Rexaintreal/HermesHandheld/images/cover.png

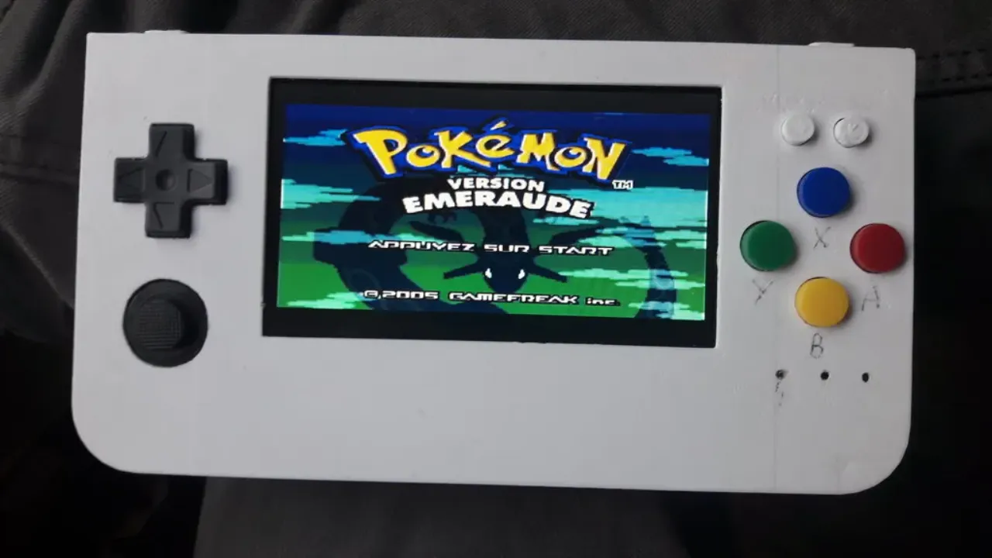
images/cover.png
