Rexaintreal/HermesHandheld/images/inspo.png

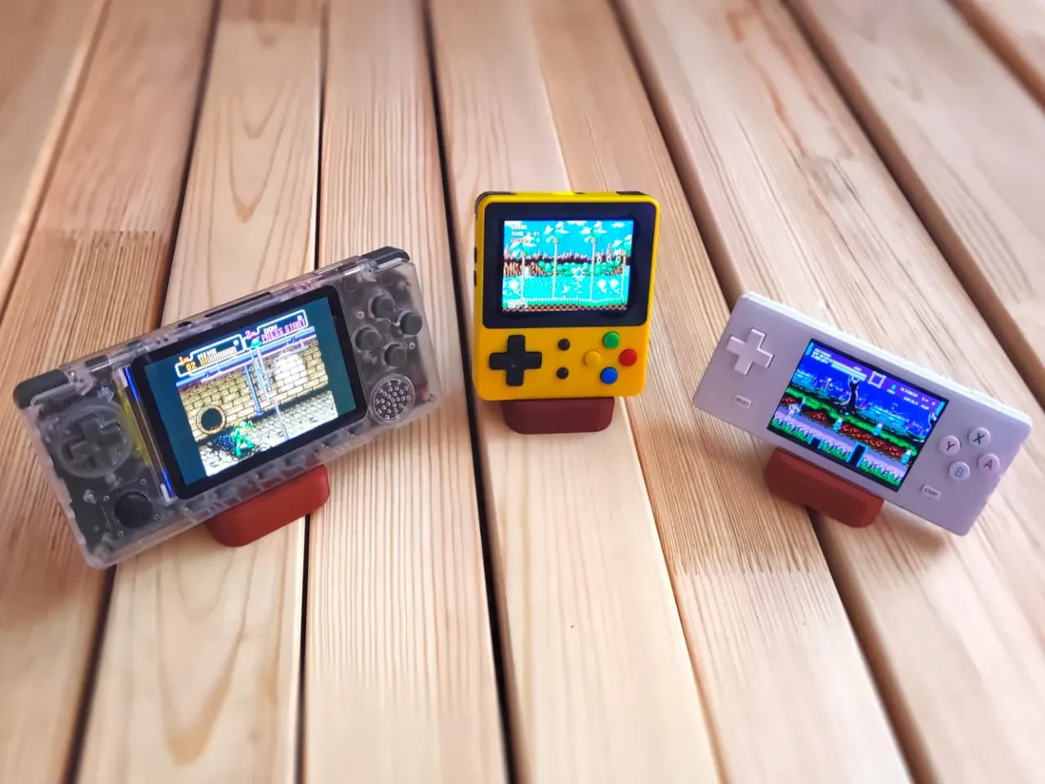
images/inspo.png
