Rexaintreal/HermesHandheld/images/Journal4image3.png

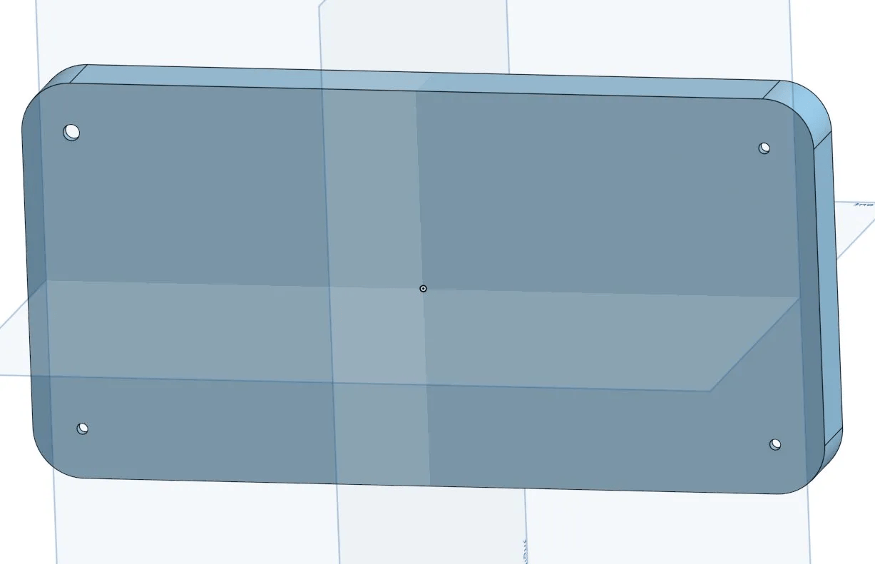
images/Journal4image3.png
