Rexaintreal/HermesHandheld/images/Journal4image4.png

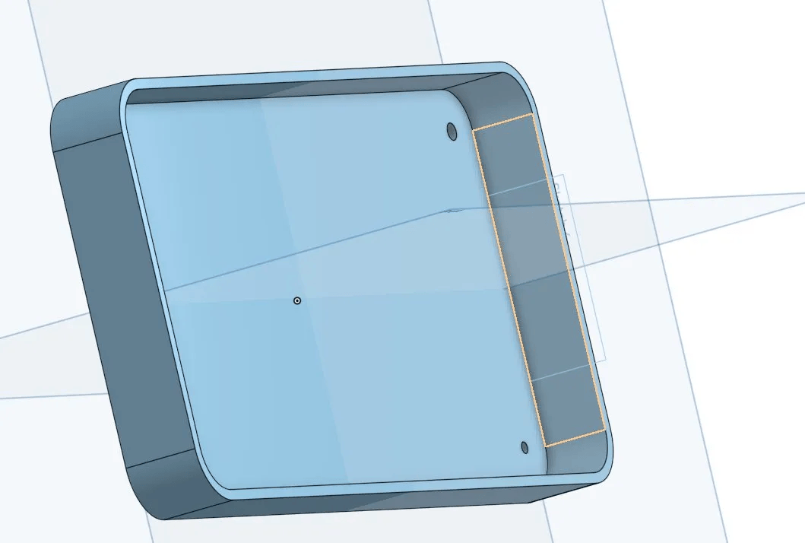
images/Journal4image4.png
