Rexaintreal/HermesHandheld/images/Journal10Image9.png

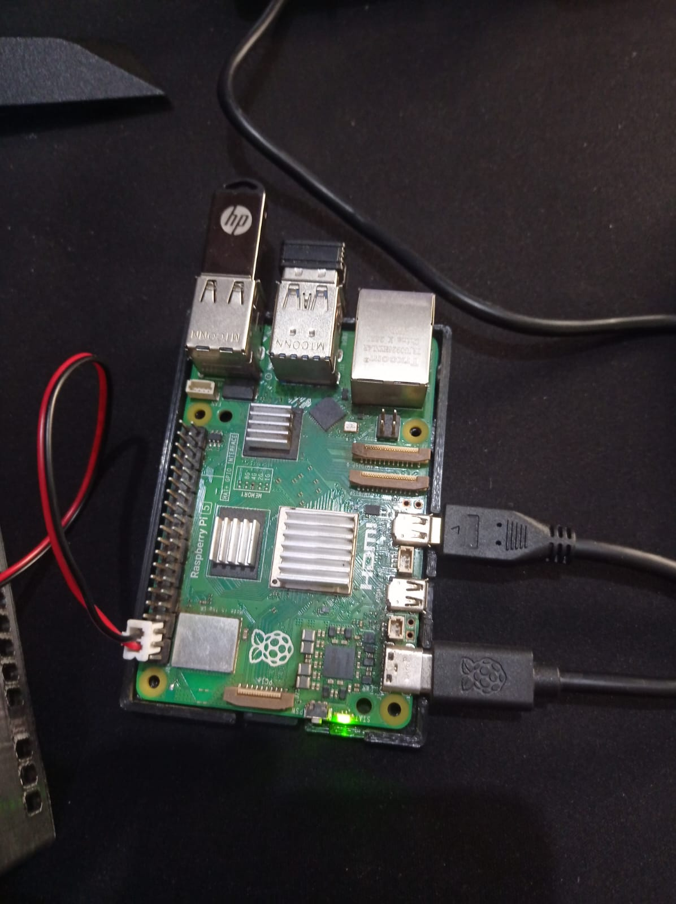
images/Journal10Image9.png
