Rexaintreal/HermesHandheld/images/Journal10Image10.png

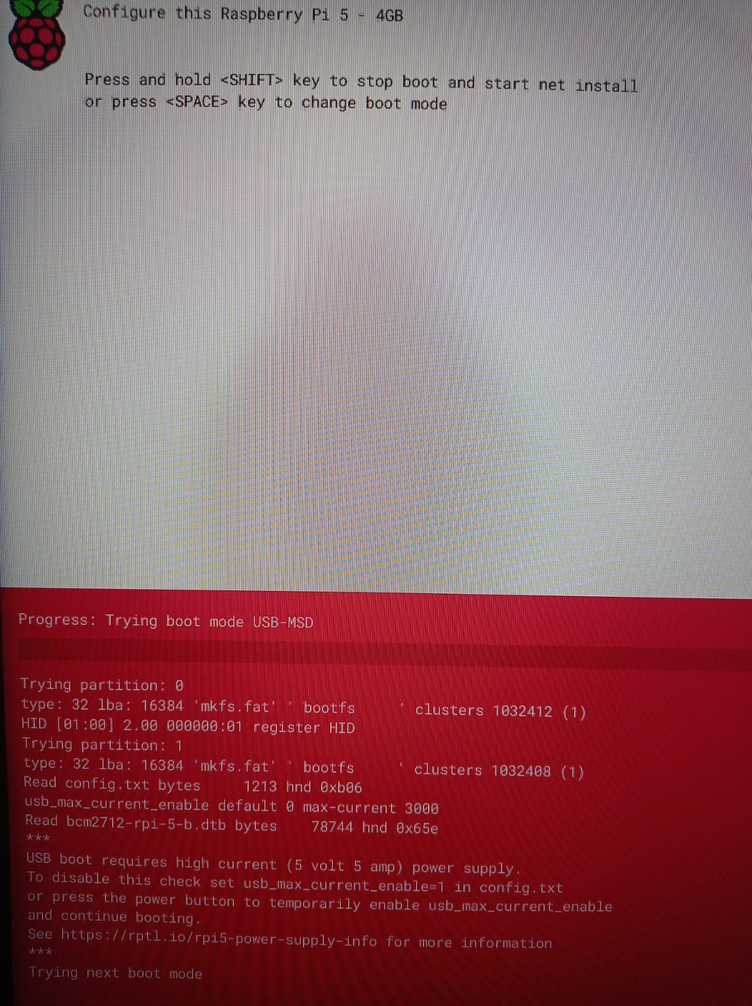
images/Journal10Image10.png
