Rexaintreal/HermesHandheld/images/Journal10Image12.png

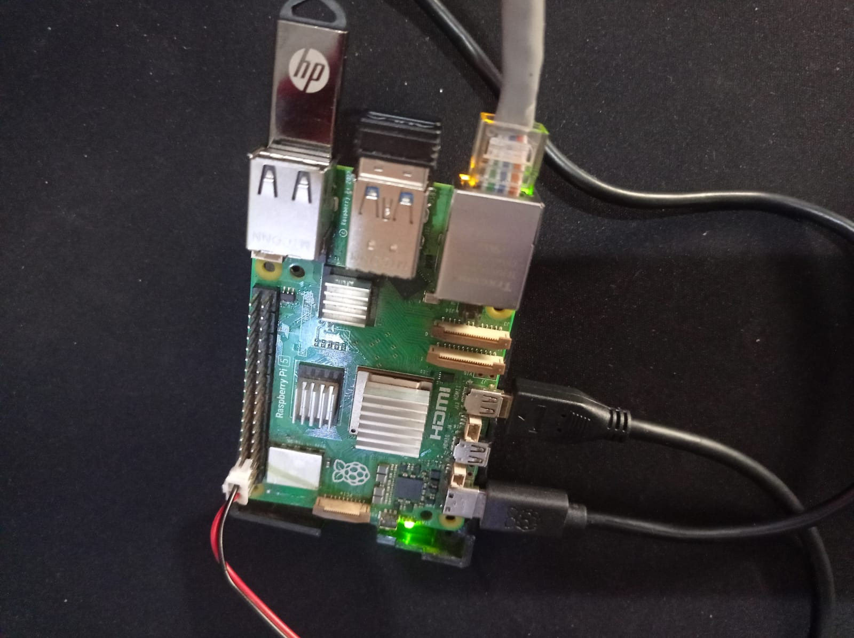
images/Journal10Image12.png
