Rexaintreal/HermesHandheld/images/Journal10Image14.png

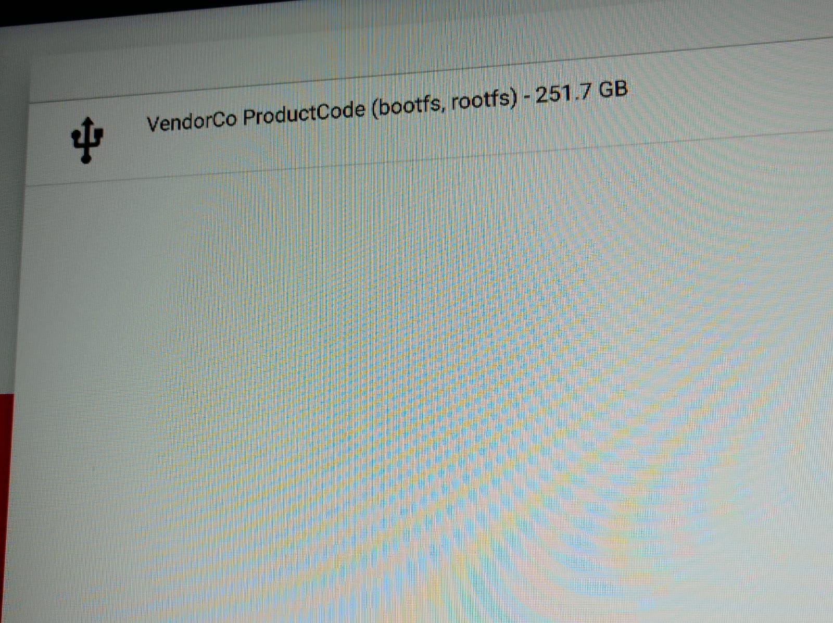
images/Journal10Image14.png
