Rexaintreal/HermesHandheld/images/Journal10Image16.png

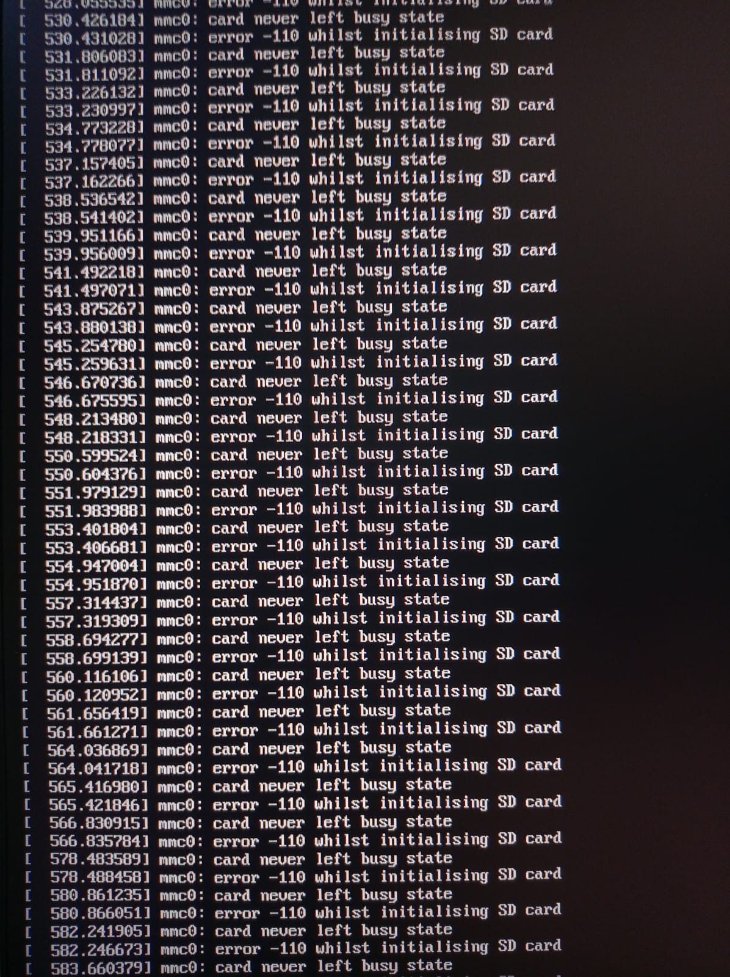
images/Journal10Image16.png
