Rexaintreal/HermesHandheld/images/Journal10Image19.png

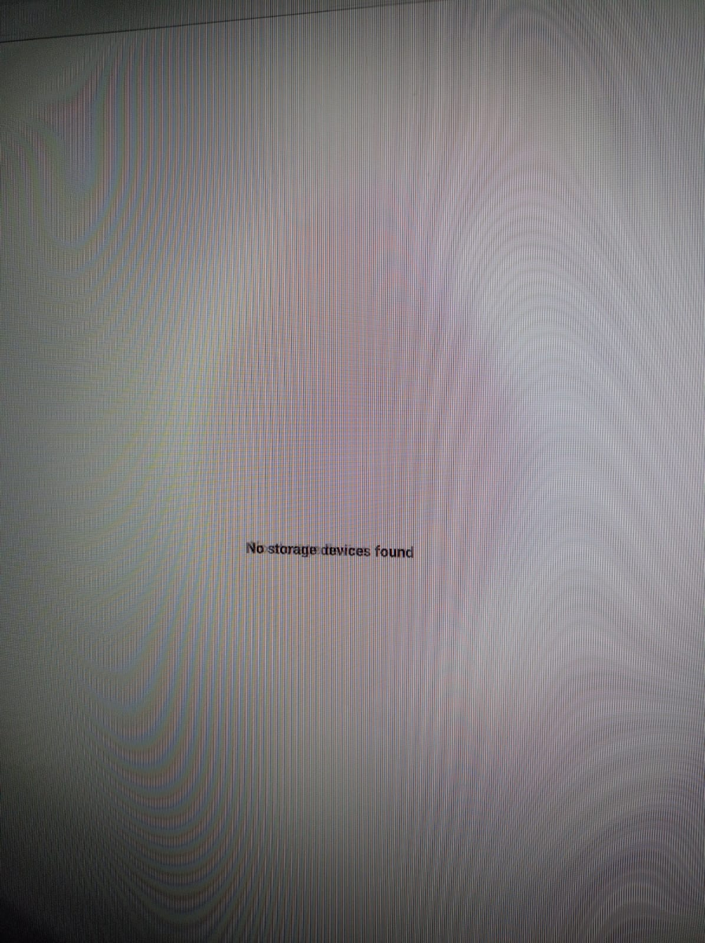
images/Journal10Image19.png
