Rexaintreal/HermesHandheld/images/Journal10Image21.png

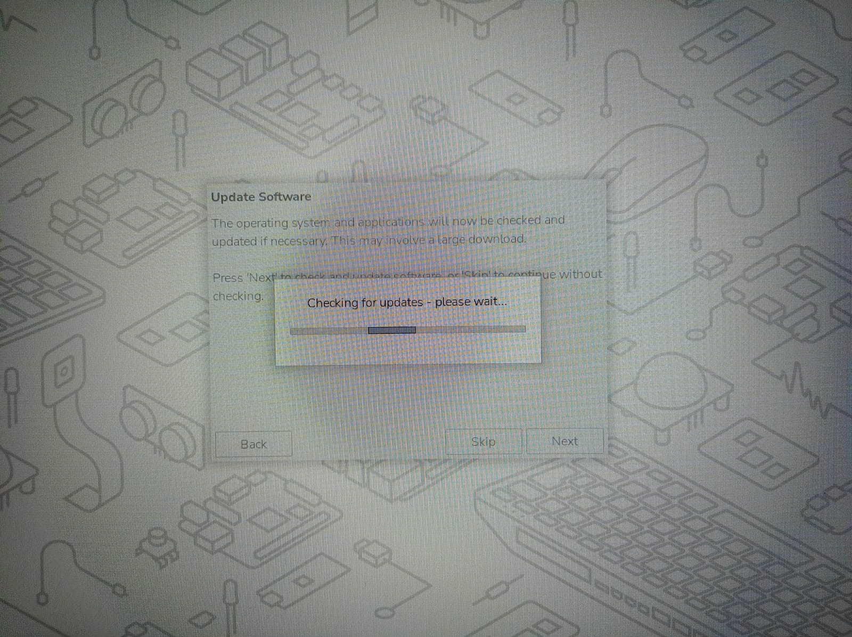
images/Journal10Image21.png
