Rexaintreal/HermesHandheld/schematics/HermesHandheld.kicad_sch

## KiCad design schematics/HermesHandheld.kicad_sch (2026-04-15)

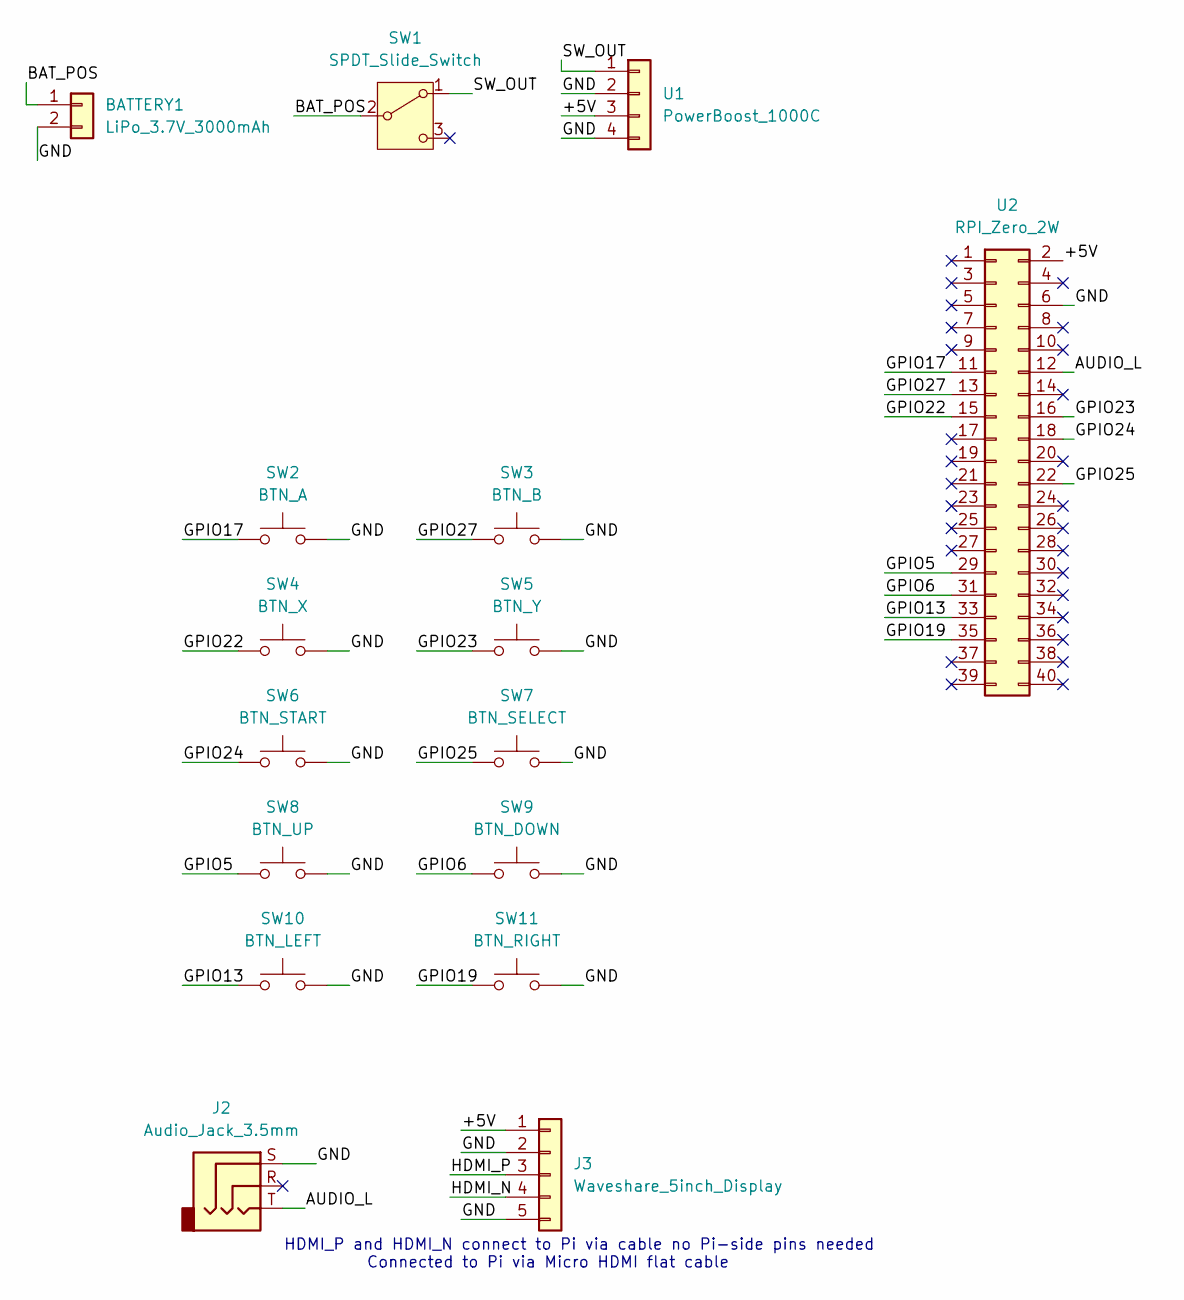
[picture p93: schematic HermesHandheld.kicad_sch]

Parts:
BATTERY1: LiPo_3.7V_3000mAh
J2: Audio_Jack_3.5mm
J3: Waveshare_5inch_Display
SW1: SPDT_Slide_Switch
SW2: BTN_A
SW3: BTN_B
SW4: BTN_X
SW5: BTN_Y
SW6: BTN_START
SW7: BTN_SELECT
SW8: BTN_UP
SW9: BTN_DOWN
SW10: BTN_LEFT
SW11: BTN_RIGHT
U1: PowerBoost_1000C
U2: RPI_Zero_2W

Connections:
+5V: J3.1, U1.3, U2.2
AUDIO_L: J2.T, U2.12
BAT_POS: BATTERY1.1, SW1.2 (B)
GND: BATTERY1.2, J2.S, J3.2, J3.5, SW2.2, SW3.2, SW4.2, SW5.2, SW6.2, SW7.2, SW8.2, SW9.2, SW10.2, SW11.2, U1.2, U1.4, U2.6
GPIO5: SW8.1, U2.29
GPIO6: SW9.1, U2.31
GPIO13: SW10.1, U2.33
GPIO17: SW2.1, U2.11
GPIO19: SW11.1, U2.35
GPIO22: SW4.1, U2.15
GPIO23: SW5.1, U2.16
GPIO24: SW6.1, U2.18
GPIO25: SW7.1, U2.22
GPIO27: SW3.1, U2.13
HDMI_N: J3.4
HDMI_P: J3.3
SW_OUT: SW1.1 (A), U1.1

Notes on the sheet:
HDMI_P and HDMI_N connect to Pi via cable no Pi-side pins needed
Connected to Pi via Micro HDMI flat cable
